ruizdiazji/microbit_hat/images/20200310_173216.jpg

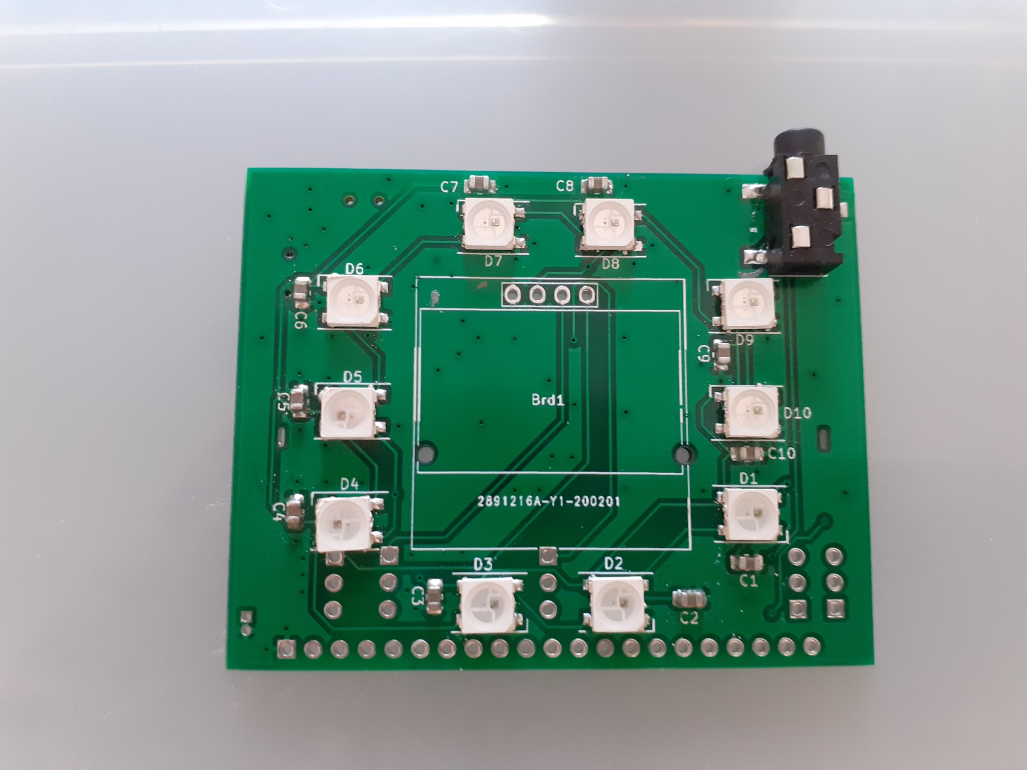
images/20200310_173216.jpg
