ruizdiazji/microbit_hat/images/20200312_163820.jpg

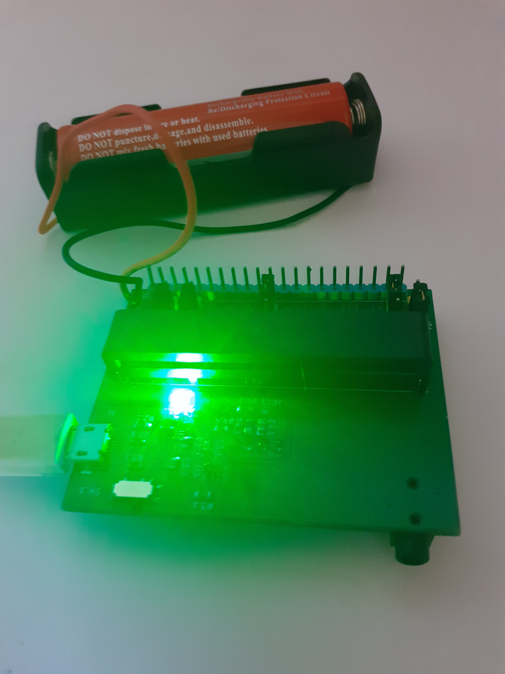
images/20200312_163820.jpg
