ruizdiazji/microbit_hat/images/20200312_163842.jpg

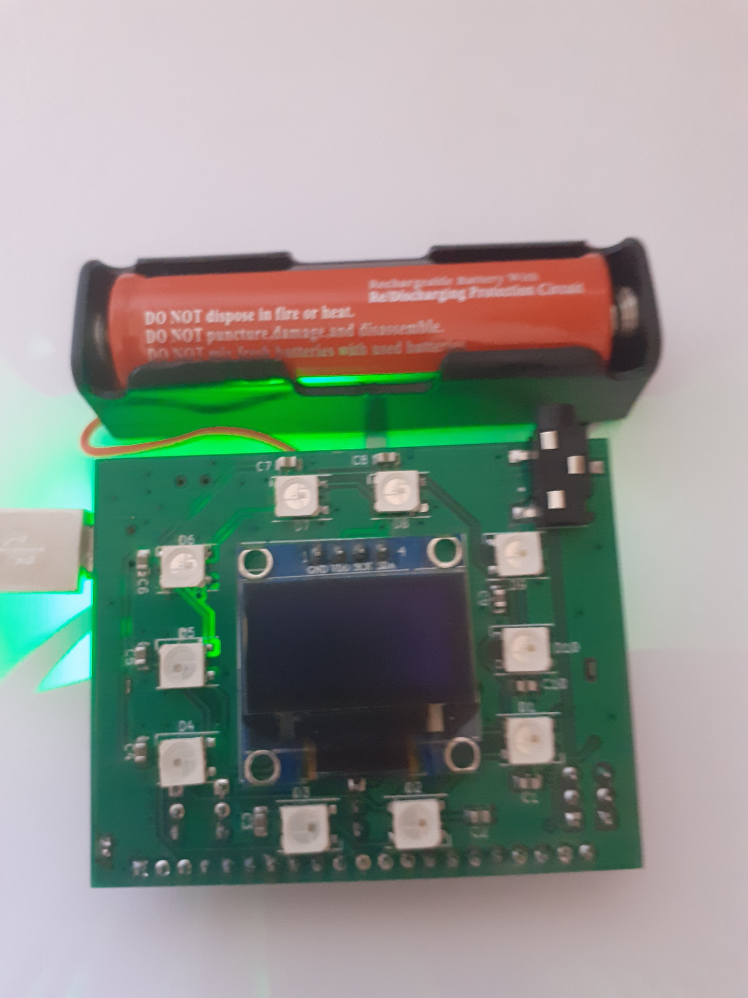
images/20200312_163842.jpg
