ruizdiazji/microbit_hat/images/20200325_122243.jpg

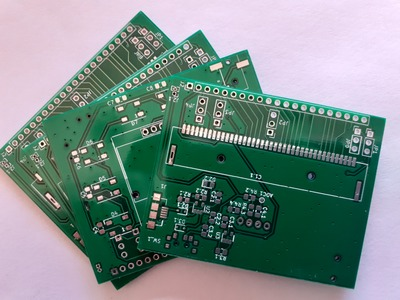
images/20200325_122243.jpg
