ruizdiazji/microbit_hat/images/20200325_122303.jpg

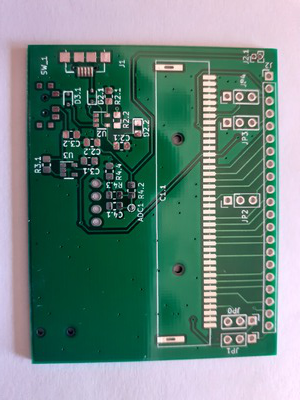
images/20200325_122303.jpg
