ruizdiazji/microbit_hat/images/20200325_122316.jpg

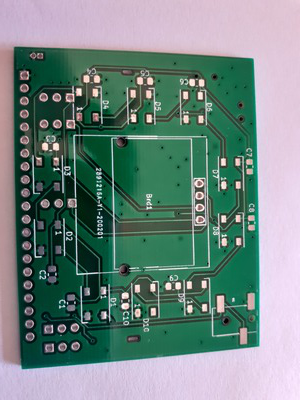
images/20200325_122316.jpg
